eziocangialosi/CarreRFN-DIY/data/dimensCarré2.png

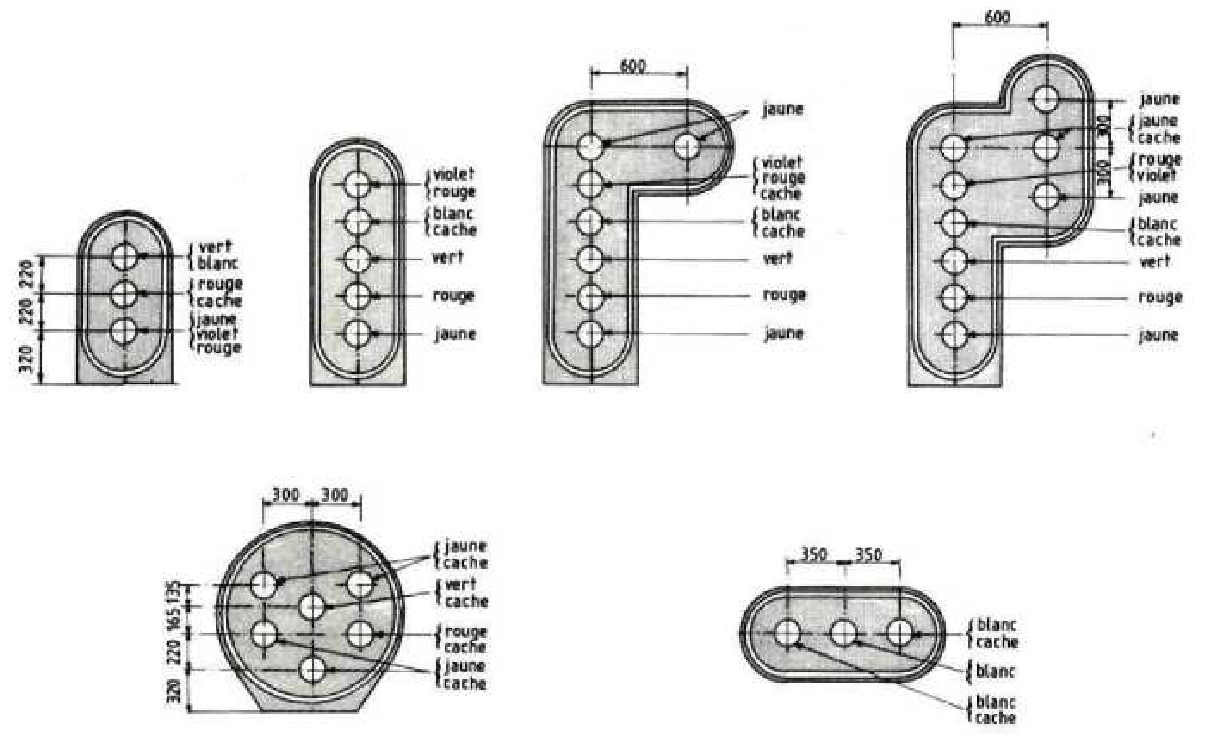
data/dimensCarré2.png
