eziocangialosi/CarreRFN-DIY/data/dimensCarré.jpg

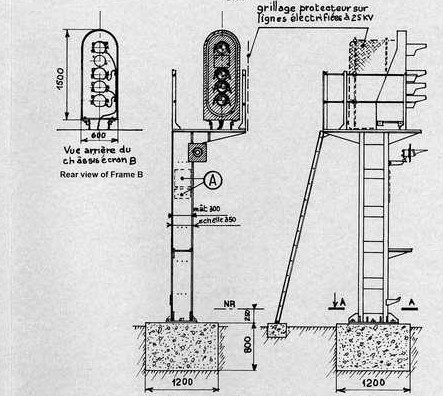
data/dimensCarré.jpg
