eziocangialosi/CarreRFN-DIY/3DModels/SLDW Files/BoucheTrou.SLDPRT

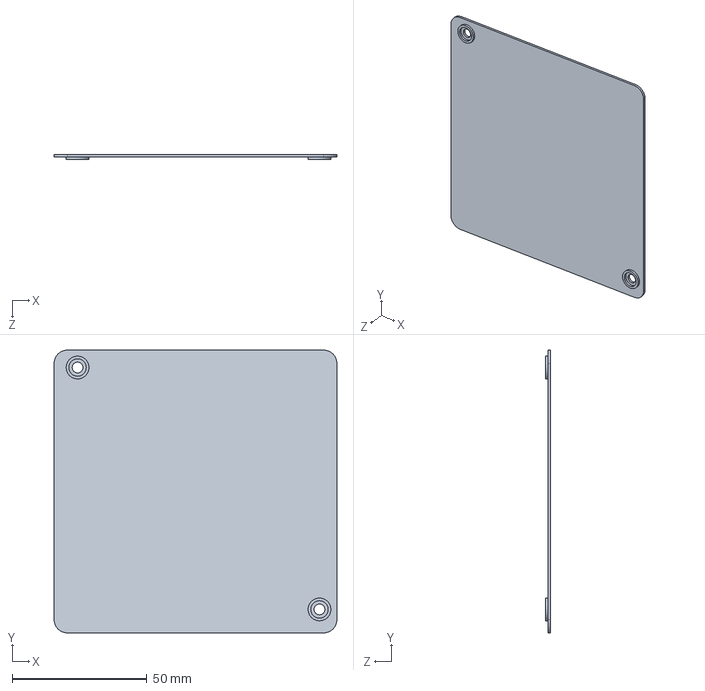
[picture p28: CAD file, 2022-06-24]
3DModels/SLDW Files/BoucheTrou.SLDPRT
105.0 x 105.0 x 2.00 mm
